Poemtech/IoTa/Software/iota-user-firmware-master/iota/cores/arduino/Arduino.h

/*
  Arduino.h - Main include file for the Arduino SDK,
  with mods for the Konekt Dash and Konekt Dash Pro

  http://konekt.io

  Copyright (c) 2015 Konekt, Inc.  All rights reserved.


  Derived from file with original copyright notice:

  Copyright (c) 2014 Arduino LLC.  All right reserved.

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
  You should have received a copy of the GNU Lesser General Public
  License along with this library; if not, write to the Free Software
  Foundation, Inc., 51 Franklin St, Fifth Floor, Boston, MA  02110-1301  USA
*/

#ifndef Arduino_h
#define Arduino_h

#include <stdbool.h>
#include <stdint.h>
#include <stdlib.h>
#include <string.h>
#include <math.h>

typedef bool boolean;
typedef uint8_t byte;
typedef uint16_t word;

// some libraries and sketches depend on this AVR stuff,
// assuming Arduino.h or WProgram.h automatically includes it...
//
#include "avr/pgmspace.h"
#include "avr/dtostrf.h"

#include "binary.h"
#include "itoa.h"

#ifdef __cplusplus
extern "C"{
#endif // __cplusplus

#include "hal/fsl_device_registers.h"

#include "wiring_constants.h"

#define clockCyclesPerMicrosecond() ( SystemCoreClock / 1000000L )
#define clockCyclesToMicroseconds(a) ( ((a) * 1000L) / (SystemCoreClock / 1000L) )
#define microsecondsToClockCycles(a) ( (a) * (SystemCoreClock / 1000000L) )
#define SystemBusClock               (SystemCoreClock / 2)

void yield( void );

/* sketch */
void setup( void );
void loop( void );

void __cxa_pure_virtual();

#ifdef __cplusplus
} // extern "C"
#endif // __cplusplus

// The following headers are for C++ only compilation
#ifdef __cplusplus
#include "WCharacter.h"

#include "WString.h"
#include "WMath.h"
#include "usb/SerialCDC.h"
#include "Wire.h"
#include "Uart.h"
#include "Dash.h"
#include "Charger.h"
#include "WVariant.h"
#include "Tone.h"

#endif // __cplusplus

// Include board variant
#include "variant.h"
#include "delay.h"
#include "wiring.h"
#include "wiring_digital.h"
#include "wiring_analog.h"
#include "wiring_shift.h"
#include "WInterrupts.h"

// undefine stdlib's abs if encountered
#ifdef abs
#undef abs
#endif // abs

#define min(a,b) ((a)<(b)?(a):(b))
#define max(a,b) ((a)>(b)?(a):(b))
#define abs(x) ((x)>0?(x):-(x))
#define constrain(amt,low,high) ((amt)<(low)?(low):((amt)>(high)?(high):(amt)))
#define round(x)     ((x)>=0?(long)((x)+0.5):(long)((x)-0.5))
#define radians(deg) ((deg)*DEG_TO_RAD)
#define degrees(rad) ((rad)*RAD_TO_DEG)
#define sq(x) ((x)*(x))

#define interrupts() __enable_irq()
#define noInterrupts() __disable_irq()

#define lowByte(w) ((uint8_t) ((w) & 0xff))
#define highByte(w) ((uint8_t) ((w) >> 8))

#define bitRead(value, bit) (((value) >> (bit)) & 0x01)
#define bitSet(value, bit) ((value) |= (1UL << (bit)))
#define bitClear(value, bit) ((value) &= ~(1UL << (bit)))
#define bitWrite(value, bit, bitvalue) (bitvalue ? bitSet(value, bit) : bitClear(value, bit))

#define bit(b) (1UL << (b))

// USB Device
//#include "USB/USBDesc.h"
//#include "USB/USBCore.h"
//#include "USB/USBAPI.h"
//#include "USB/USB_host.h"

#endif // Arduino_h
