Poemtech/IoTa/Software/iota-user-firmware-master/iota/variants/iota/variant.h

/*
  variant.h

  http://konekt.io

  Copyright (c) 2015 Konekt, Inc.  All rights reserved.

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
  You should have received a copy of the GNU Lesser General Public
  License along with this library; if not, write to the Free Software
  Foundation, Inc., 51 Franklin St, Fifth Floor, Boston, MA  02110-1301  USA
*/

#pragma once

#include "WVariant.h"

#define PINS_COUNT              (37u)

#define D01      1
#define D02      3
#define D03      0
#define D04     16
#define D05     17
#define D06      6
#define D07     18
#define D08      7
#define D09     14
#define D10     15
#define D11     13
#define D12     11
#define D13     10
#define D14     12
#define D15      5
#define D16      9
#define D17      2
#define D18      8
#define D19     19
#define D26     30
#define D27     31
#define D28     32
#define D29     33
#define D30     34

#define A01     16
#define A02     18
#define A03     14
#define A04     15
#define A05      5
#define A06     19
#define A07     35
#define A08     32
#define A09     36
#define A10     20

//Arduino compatibility
#define A0      16
#define A1      18
#define A2       5
#define A3      19
#define A4      14
#define A5      15
#define A6      20

#define R03      1
#define R04      3
#define R05      0
#define R06     16
#define R07     17
#define R08      6
#define R09     18
#define R10      7
//-----------------
#define R11     29
#define R13     30
#define R14     31
#define R15     32
#define R16     33
#define R17     34
#define R18     36

#define L03     14
#define L04     15
#define L05     13
#define L06     11
#define L07     10
#define L08     12
#define L09      5
#define L10      9
#define L11      2
#define L12      8
#define L13     19
#define L14     20
#define L18     35

#define SPI_SCK             13
#define SPI_SOUT            11
#define SPI_SIN             12
#define SPI_SS              10

#define ALT_SPI_SCK         13
#define ALT_SPI_SOUT        30
#define ALT_SPI_SIN         31
#define ALT_SPI_SS          33

#ifdef ALT_SPI
#define MOSI                ALT_SPI_SOUT
#define MISO                ALT_SPI_SIN
#define SCK                 ALT_SPI_SCK
#define SS                  ALT_SPI_SS
#else
#define MOSI                SPI_SOUT
#define MISO                SPI_SIN
#define SCK                 SPI_SCK
#define SS                  SPI_SS
#endif

#define BOARD_SPI_DEFAULT_SS    SS

#define USB_STR_PRODUCT_SIZE  (22)

#define WKUP0                       0
#define WKUP_L04                    0
#define WKUP_D10                    0
#define WKUP4                       4
#define WKUP_L12                    4
#define WKUP_D18                    4
#define WKUP5                       5
#define WKUP_L13                    5
#define WKUP_D19                    5
#define WKUP6                       6
#define WKUP_R07                    6
#define WKUP_D05                    6
#define WKUP10                      10
#define WKUP_R13                    10
#define WKUP_D26                    10
#define WKUP11                      11
#define WKUP_R17                    11
#define WKUP_D30                    11
#define WKUP12                      12
#define WKUP_R16                    12
#define WKUP_D29                    12
#define WKUP13                      13
#define WKUP_L06                    13
#define WKUP_D12                    13
#define WKUP14                      14
#define WKUP_R04                    14
#define WKUP_D02                    14
#define WKUP15                      15
#define WKUP_R05                    15
#define WKUP_D03                    15
#define WKUP16                      16
#define WKUP_TIMER                  16
#define WKUP21                      21
#define WKUP_ALARM                  21

void initVariant(void);
