Poemtech/IoTa/Software/iota-user-firmware-master/iota/cores/arduino/Uart.cpp

/*
  Uart.cpp - Implements Uart class, with mods for the
  Konekt Dash and Konekt Dash Pro family

  http://konekt.io

  Copyright (c) 2015 Konekt, Inc.  All rights reserved.


  Derived from file with original copyright notice:

  Copyright (c) 2015 Arduino LLC.  All right reserved.

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
  You should have received a copy of the GNU Lesser General Public
  License along with this library; if not, write to the Free Software
  Foundation, Inc., 51 Franklin St, Fifth Floor, Boston, MA  02110-1301  USA
*/

#include "Uart.h"
#include "Arduino.h"
#include "hal/fsl_uart_hal.h"

Uart::Uart(UART_Type * instance, sim_clock_gate_name_t gate_name, uint32_t clock,
    IRQn_Type irqNumber, uint32_t rx, uint32_t tx)
{
    this->instance = instance;
    this->gate_name = gate_name;
    this->clock = clock;
    this->irqNumber = irqNumber;
    this->rx = rx;
    this->tx = tx;
}

void Uart::end()
{
    UART_HAL_Init(instance);
    NVIC_DisableIRQ(irqNumber);
    SIM_HAL_DisableClock(SIM, gate_name);
    rxBuffer.clear();
}

int Uart::available()
{
    return rxBuffer.available();
}

int Uart::peek()
{
    return rxBuffer.peek();
}

int Uart::read()
{
    return rxBuffer.read_char();
}

void Uart::begin(uint32_t baudrate)
{
    begin(baudrate, SERIAL_8N1);
}

void Uart::begin(unsigned long baudrate, uint16_t config)
{
    singleWire = (config & HARDSER_DUPLEX_MASK) == HARDSER_DUPLEX_HALF;

    SIM_HAL_EnableClock(SIM, gate_name);

    if(!singleWire) {
        PORT_CLOCK_ENABLE(rx);
        PORT_SET_MUX_UART(rx);
    }

    PORT_CLOCK_ENABLE(tx);
    PORT_SET_MUX_UART(tx);

#if FSL_FEATURE_SOC_UART_COUNT
    UART_HAL_Init(instance);
    UART_HAL_SetBaudRate(instance, clock, baudrate);
    UART_HAL_SetBitCountPerChar(instance, kUart8BitsPerChar);

    uart_parity_mode_t p = kUartParityDisabled;
    switch(config & HARDSER_PARITY_MASK) {
        case HARDSER_PARITY_EVEN: p = kUartParityEven; break;
        case HARDSER_PARITY_ODD: p = kUartParityOdd; break;
        case HARDSER_PARITY_NONE:
        default: p = kUartParityDisabled; break;
    }
    parity = (p != kUartParityDisabled);
    UART_HAL_SetParityMode(instance, p);

#if FSL_FEATURE_UART_HAS_STOP_BIT_CONFIG_SUPPORT
    UART_HAL_SetStopBitCount(instance,
        (config & HARDSER_STOP_BIT_MASK) == HARDSER_STOP_BIT_2 ?
        kUartTwoStopBit : kUartOneStopBit);
#endif

    if(singleWire) {
        UART_HAL_SetLoopCmd(instance, true);
        UART_HAL_SetReceiverSource(instance, kUartSingleWire);
        UART_HAL_SetTransmitterDir(instance, kUartSinglewireTxdirIn);
    }

    UART_HAL_SetIntMode(instance, kUartIntRxDataRegFull, true);
    NVIC_EnableIRQ(irqNumber);

    UART_HAL_EnableTransmitter(instance);
    UART_HAL_EnableReceiver(instance);
#endif
}

void Uart::flush()
{
    rxBuffer.clear();
}

void Uart::waitToEmpty()
{
#if FSL_FEATURE_SOC_UART_COUNT
    if(!SIM_HAL_GetGateCmd(SIM, gate_name)) return;
    uint32_t start = millis();
    while(!(UART_RD_S1(instance) & (UART_S1_TDRE_MASK)))
    {
        if(millis() - start > 10)
            return;
    }
    while(!(UART_RD_S1(instance) & (UART_S1_TC_MASK)))
    {
        if(millis() - start > 10)
            break;
    }
#endif
}

void Uart::IrqHandler()
{
#if FSL_FEATURE_SOC_UART_COUNT
    while(UART_RD_S1_RDRF(instance)) {
        uint8_t b = UART_RD_D(instance);
        if(parity)
            rxBuffer.store_char(b&0x7F);
        else
            rxBuffer.store_char(b);
    }
#endif
}

size_t Uart::write(const uint8_t data)
{
#if FSL_FEATURE_SOC_UART_COUNT
    if(!SIM_HAL_GetGateCmd(SIM, gate_name)) return 0;
    uint32_t start = millis();

    while (!UART_BRD_S1_TDRE(instance))
    {
        if(millis() - start > 10)
            return 0;
    }

    if(singleWire) {
        UART_HAL_SetTransmitterDir(instance, kUartSinglewireTxdirOut);
    }

    UART_HAL_Putchar(instance, data);

    if(singleWire) {
        uint32_t start = millis();
        while (!UART_BRD_S1_TC(instance))
        {
            if(millis() - start > 10) {
                UART_HAL_SetTransmitterDir(instance, kUartSinglewireTxdirIn);
                return 0;
            }
        }
        UART_HAL_SetTransmitterDir(instance, kUartSinglewireTxdirIn);
    }
    return 1;
#endif

    return 0;
}
