Poemtech/IoTa/Software/iota-system-firmware-master/iota_system/cores/arduino/hal/fsl_sim_hal_MKL17Z4.c

/*
* Copyright (c) 2013 - 2014, Freescale Semiconductor, Inc.
* All rights reserved.
*
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
* o Neither the name of Freescale Semiconductor, Inc. nor the names of its
*   contributors may be used to endorse or promote products derived from this
*   software without specific prior written permission.
*
* THIS SOFTWARE IS PROVIDED BY THE COPYRIGHT HOLDERS AND CONTRIBUTORS "AS IS" AND
* ANY EXPRESS OR IMPLIED WARRANTIES, INCLUDING, BUT NOT LIMITED TO, THE IMPLIED
* WARRANTIES OF MERCHANTABILITY AND FITNESS FOR A PARTICULAR PURPOSE ARE
* DISCLAIMED. IN NO EVENT SHALL THE COPYRIGHT HOLDER OR CONTRIBUTORS BE LIABLE FOR
* ANY DIRECT, INDIRECT, INCIDENTAL, SPECIAL, EXEMPLARY, OR CONSEQUENTIAL DAMAGES
* (INCLUDING, BUT NOT LIMITED TO, PROCUREMENT OF SUBSTITUTE GOODS OR SERVICES;
* LOSS OF USE, DATA, OR PROFITS; OR BUSINESS INTERRUPTION) HOWEVER CAUSED AND ON
* ANY THEORY OF LIABILITY, WHETHER IN CONTRACT, STRICT LIABILITY, OR TORT
* (INCLUDING NEGLIGENCE OR OTHERWISE) ARISING IN ANY WAY OUT OF THE USE OF THIS
* SOFTWARE, EVEN IF ADVISED OF THE POSSIBILITY OF SUCH DAMAGE.
*/

#include <stdint.h>
#include <stdlib.h>
#include <stdbool.h>
#include "fsl_device_registers.h"
#include "fsl_sim_hal.h"
#include "fsl_sim_hal_MKL17Z4.h"

/*******************************************************************************
* Definitions
******************************************************************************/

/*******************************************************************************
* APIs
******************************************************************************/

/*FUNCTION**********************************************************************
*
* Function Name : CLOCK_HAL_SetOutDiv
* Description   : Set all clock out dividers setting at the same time
* This function will set the setting for all clock out dividers.
*
*END**************************************************************************/
void CLOCK_HAL_SetOutDiv(SIM_Type * base,
                         uint8_t outdiv1,
                         uint8_t outdiv2,
                         uint8_t outdiv3,
                         uint8_t outdiv4)
{
    uint32_t clkdiv1 = 0;

    clkdiv1 |= SIM_CLKDIV1_OUTDIV1(outdiv1);
    clkdiv1 |= SIM_CLKDIV1_OUTDIV4(outdiv4);

    SIM_WR_CLKDIV1(base, clkdiv1);
}

/*FUNCTION**********************************************************************
 *
 * Function Name : CLOCK_HAL_GetOutDiv
 * Description   : Get all clock out dividers setting at the same time
 * This function will get the setting for all clock out dividers.
 *
 *END**************************************************************************/
void CLOCK_HAL_GetOutDiv(SIM_Type * base,
                         uint8_t *outdiv1,
                         uint8_t *outdiv2,
                         uint8_t *outdiv3,
                         uint8_t *outdiv4)
{
    *outdiv1 = SIM_BRD_CLKDIV1_OUTDIV1(base);
    *outdiv2 = 0U;
    *outdiv3 = 0U;
    *outdiv4 = SIM_BRD_CLKDIV1_OUTDIV4(base);
}

/*FUNCTION**********************************************************************
 *
 * Function Name : CLOCK_HAL_SetLpuartSrc
 * Description   : Set the clock selection of LPUART.
 * This function sets the clock selection of LPUART.
 *
 *END**************************************************************************/
void CLOCK_HAL_SetLpuartSrc(SIM_Type * base,
                            uint32_t instance,
                            clock_lpuart_src_t setting)
{
    assert(instance < LPUART_INSTANCE_COUNT);

    if (0u == instance)
    {
        SIM_BWR_SOPT2_LPUART0SRC(base, setting);
    }
    else
    {
        SIM_BWR_SOPT2_LPUART1SRC(base, setting);
    }
}

/*FUNCTION**********************************************************************
 *
 * Function Name : CLOCK_HAL_GetLpuartSrc
 * Description   : Get the clock selection of LPUART.
 * This function gets the clock selection of LPUART.
 *
 *END**************************************************************************/
clock_lpuart_src_t CLOCK_HAL_GetLpuartSrc(SIM_Type * base,
                                          uint32_t instance)
{
    assert(instance < LPUART_INSTANCE_COUNT);

    if (0u == instance)
    {
        return (clock_lpuart_src_t)SIM_BRD_SOPT2_LPUART0SRC(base);
    }
    else
    {
        return (clock_lpuart_src_t)SIM_BRD_SOPT2_LPUART1SRC(base);
    }
}

/*FUNCTION**********************************************************************
 *
 * Function Name : SIM_HAL_SetTpmChSrcMode
 * Description   : Sets the Timer/PWM x channel y input capture source.
 *
 *END**************************************************************************/
void SIM_HAL_SetTpmChSrcMode(SIM_Type * base,
                             uint32_t instance,
                             uint8_t channel,
                             sim_tpm_ch_src_t select)
{
    assert(instance < TPM_INSTANCE_COUNT);

    if(instance == 1)
    {
        SIM_BWR_SOPT4_TPM1CH0SRC(base, select);
    }
    else if(instance == 2)
    {
        SIM_BWR_SOPT4_TPM2CH0SRC(base, select);
    }
}

/*FUNCTION**********************************************************************
 *
 * Function Name : SIM_HAL_SetTpmChSrcMode
 * Description   : Sets the Timer/PWM x channel y input capture source.
 *
 *END**************************************************************************/
sim_tpm_ch_src_t SIM_HAL_GetTpmChSrcMode(SIM_Type * base,
                                         uint32_t instance,
                                         uint8_t channel)
{
    assert(instance < TPM_INSTANCE_COUNT);

    sim_tpm_ch_src_t retValue = (sim_tpm_ch_src_t)0;

    if(instance == 1)
    {
        retValue = (sim_tpm_ch_src_t)SIM_BRD_SOPT4_TPM1CH0SRC(base);
    }
    else if(instance == 2)
    {
        retValue = (sim_tpm_ch_src_t)SIM_BRD_SOPT4_TPM2CH0SRC(base);
    }

    return retValue;
}

/*FUNCTION**********************************************************************
*
* Function Name : SIM_HAL_SetLpuartRxSrcMode
* Description   : Sets the LPUARTx receive data source select setting.
*
*END**************************************************************************/
void SIM_HAL_SetLpuartRxSrcMode(SIM_Type * base,
                                uint32_t instance,
                                sim_lpuart_rxsrc_t select)
{
    assert(instance < LPUART_INSTANCE_COUNT);

    if (0 == instance)
    {
        SIM_BWR_SOPT5_LPUART0RXSRC(base, select);
    }
    else
    {
        SIM_BWR_SOPT5_LPUART1RXSRC(base, select);
    }
}

/*FUNCTION**********************************************************************
*
* Function Name : SIM_HAL_GetLpuartRxSrcMode
* Description   : Gets the LPUARTx receive data source select setting.
*
*END**************************************************************************/
sim_lpuart_rxsrc_t SIM_HAL_GetLpuartRxSrcMode(SIM_Type * base, uint32_t instance)
{
    assert(instance < LPUART_INSTANCE_COUNT);

    if (0 == instance)
    {
        return (sim_lpuart_rxsrc_t)SIM_BRD_SOPT5_LPUART0RXSRC(base);
    }
    else
    {
        return (sim_lpuart_rxsrc_t)SIM_BRD_SOPT5_LPUART1RXSRC(base);
    }
}

/*FUNCTION**********************************************************************
*
* Function Name : SIM_HAL_SetLpuartTxSrcMode
* Description   : Sets the LPUARTx transmit data source select setting.
*
*END**************************************************************************/
void SIM_HAL_SetLpuartTxSrcMode(SIM_Type * base,
                                uint32_t instance,
                                sim_lpuart_txsrc_t select)
{
    assert(instance < LPUART_INSTANCE_COUNT);

    if (0 == instance)
    {
        SIM_BWR_SOPT5_LPUART0TXSRC(base, select);
    }
    else
    {
        SIM_BWR_SOPT5_LPUART1TXSRC(base, select);
    }
}

/*FUNCTION**********************************************************************
*
* Function Name : SIM_HAL_SetLpuartTxSrcMode
* Description   : Sets the LPUARTx transmit data source select setting.
*
*END**************************************************************************/
sim_lpuart_txsrc_t SIM_HAL_GetLpuartTxSrcMode(SIM_Type * base, uint32_t instance)
{
    assert(instance < LPUART_INSTANCE_COUNT);

    if (0 == instance)
    {
        return (sim_lpuart_txsrc_t)SIM_BRD_SOPT5_LPUART0TXSRC(base);
    }
    else
    {
        return (sim_lpuart_txsrc_t)SIM_BRD_SOPT5_LPUART1TXSRC(base);
    }
}

/*FUNCTION**********************************************************************
*
* Function Name : SIM_HAL_SetLpuartOpenDrainCmd
* Description   : This function enables/disables the LPUARTx Open Drain.
*
*END**************************************************************************/
void SIM_HAL_SetLpuartOpenDrainCmd(SIM_Type * base, uint32_t instance, bool enable)
{
    assert(instance < LPUART_INSTANCE_COUNT);

    if (0 == instance)
    {
        SIM_BWR_SOPT5_LPUART0ODE(base, enable ? 1 : 0);
    }
    else
    {
        SIM_BWR_SOPT5_LPUART1ODE(base, enable ? 1 : 0);
    }
}

/*FUNCTION**********************************************************************
*
* Function Name : SIM_HAL_GetLpuartOpenDrainCmd
* Description   : This function gets the LPUARTx Open Drain setting.
*
*END**************************************************************************/
bool SIM_HAL_GetLpuartOpenDrainCmd(SIM_Type * base, uint32_t instance)
{
    assert(instance < LPUART_INSTANCE_COUNT);

    if (0 == instance)
    {
        return (bool)SIM_BRD_SOPT5_LPUART0ODE(base);
    }
    else
    {
        return (bool)SIM_BRD_SOPT5_LPUART1ODE(base);
    }
}

/*FUNCTION**********************************************************************
*
* Function Name : SIM_HAL_SetAdcTriggerModeOneStep
* Description   : Set ADCx trigger setting.
* This function sets ADC alternate trigger, pre-trigger mode and trigger mode.
*
*END**************************************************************************/
void SIM_HAL_SetAdcTriggerModeOneStep(SIM_Type * base,
                                      uint32_t instance,
                                      bool    altTrigEn,
                                      sim_adc_pretrg_sel_t preTrigSel,
                                      sim_adc_trg_sel_t trigSel)
{
    assert(instance < ADC_INSTANCE_COUNT);

    SIM_BWR_SOPT7_ADC0ALTTRGEN(base, altTrigEn ? 1 : 0);
    SIM_BWR_SOPT7_ADC0PRETRGSEL(base, preTrigSel);

    if (altTrigEn)
    {
        SIM_BWR_SOPT7_ADC0TRGSEL(base, trigSel);
    }

}

/*FUNCTION**********************************************************************
*
* Function Name : SIM_HAL_SetTpmExternalClkPinSelMode
* Description	 : Set Timer/PWM x external clock pin select setting
* This function will select the source of Timer/PWM x external clock pin select
* 
*END**************************************************************************/
void SIM_HAL_SetTpmExternalClkPinSelMode(SIM_Type * base,
                                         uint32_t instance,
                                         sim_tpm_clk_sel_t select)
{
    assert (instance < TPM_INSTANCE_COUNT);
    
    switch (instance)
    {
    case 0:
        SIM_BWR_SOPT4_TPM0CLKSEL(base, select);
        break;
    case 1:
        SIM_BWR_SOPT4_TPM1CLKSEL(base, select);
        break;
    default:
        break;
    }
}

/*FUNCTION**********************************************************************
*
* Function Name : SIM_HAL_GetTpmExternalClkPinSelMode
* Description	 : Get Timer/PWM x external clock pin select setting
* This function will get Timer/PWM x external clock pin select setting.
* 
*END**************************************************************************/
sim_tpm_clk_sel_t SIM_HAL_GetTpmExternalClkPinSelMode(SIM_Type * base, uint32_t instance)
{
    sim_tpm_clk_sel_t retValue = (sim_tpm_clk_sel_t)0;
    
    assert (instance < TPM_INSTANCE_COUNT);
    
    switch (instance)
    {
    case 0:
        retValue = (sim_tpm_clk_sel_t)SIM_BRD_SOPT4_TPM0CLKSEL(base);
        break;
    case 1:
        retValue = (sim_tpm_clk_sel_t)SIM_BRD_SOPT4_TPM1CLKSEL(base);
        break;
    default:
        break;
    }
    
    return retValue;
}

/*******************************************************************************
* EOF
******************************************************************************/
